kholia/Easy-Transceiver/BoB-For-2003/Screenshot_2022-04-22_13-50-55.png

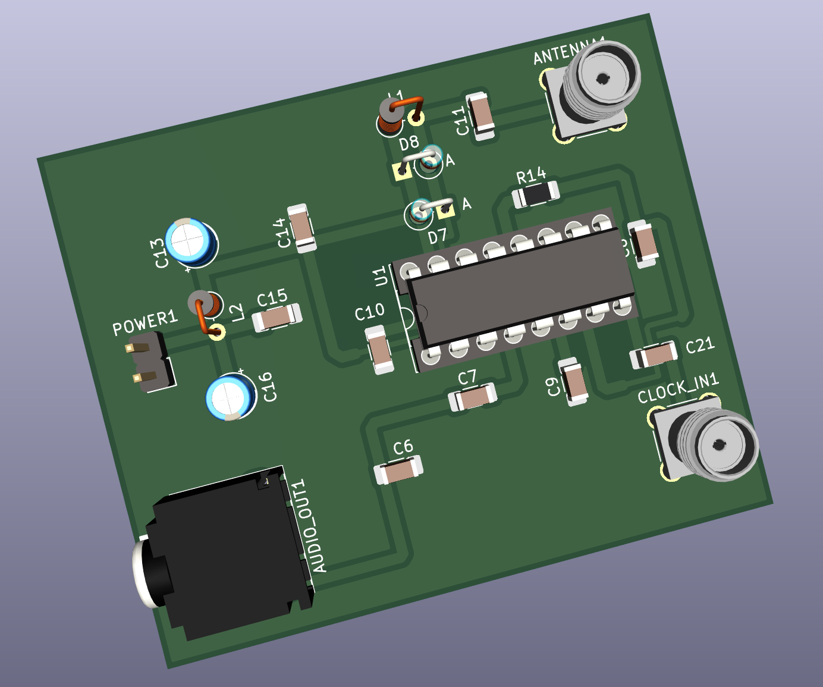
BoB-For-2003/Screenshot_2022-04-22_13-50-55.png
