kholia/Easy-Transceiver/HPF-BCI-Filter-RX/QUCS-filter/Screenshot_2022-02-17_18-40-45.png

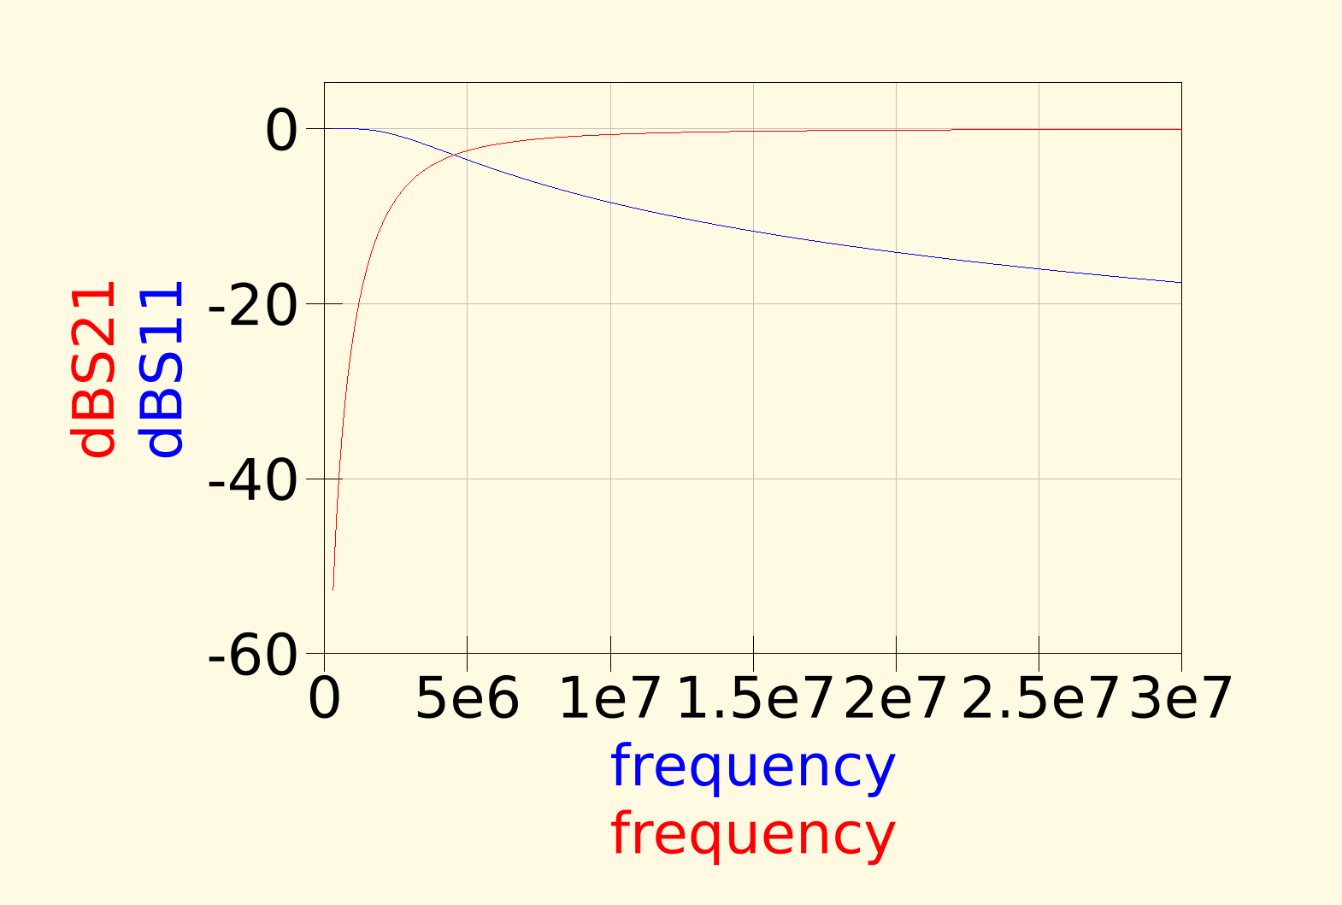
HPF-BCI-Filter-RX/QUCS-filter/Screenshot_2022-02-17_18-40-45.png
