kholia/Easy-Transceiver/images/1-CHANNEL-RELAY-MODULE-5V-Interfacing.jpg

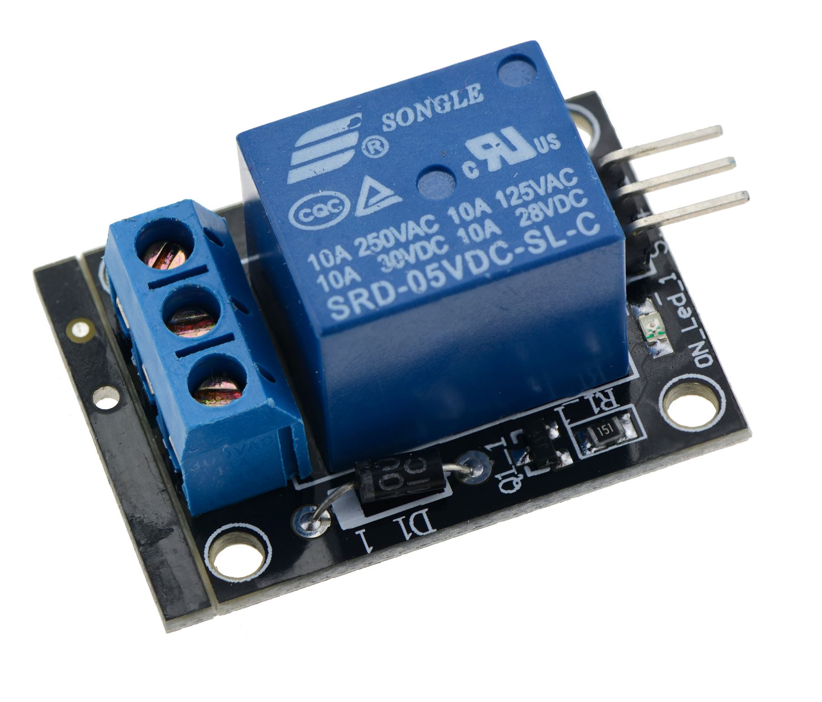
images/1-CHANNEL-RELAY-MODULE-5V-Interfacing.jpg
