kholia/Easy-Transceiver/images/3.5mm-Female-Stereo-Audio-Socket-Headphone-Jack-Connector-5-Pin-PCB-Mount_1.jpg

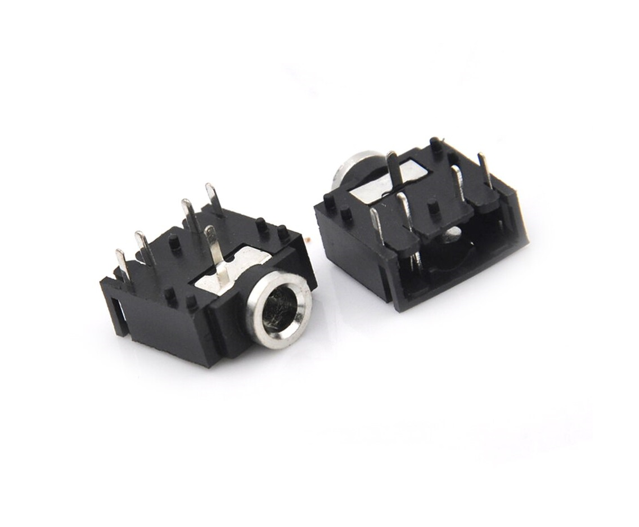
images/3.5mm-Female-Stereo-Audio-Socket-Headphone-Jack-Connector-5-Pin-PCB-Mount_1.jpg
