kholia/Easy-Transceiver/images/428.jpg

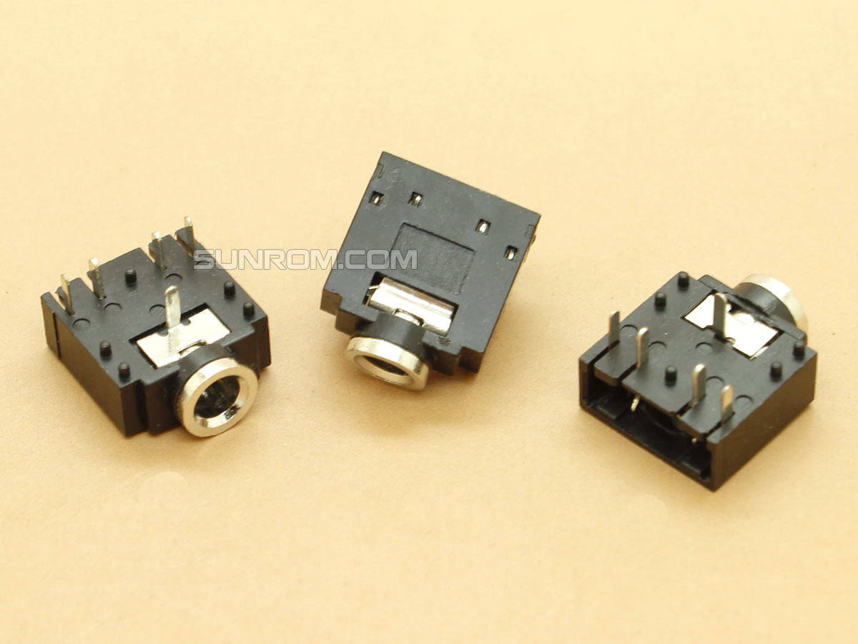
images/428.jpg
