kholia/Easy-Transceiver/images/Arduino-Nano.jpg

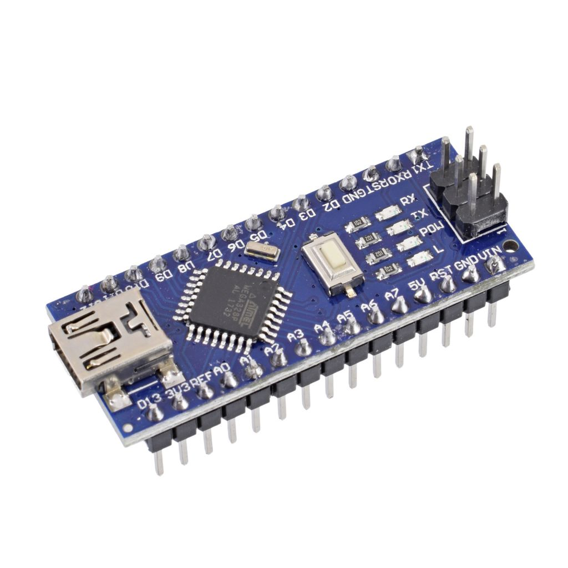
images/Arduino-Nano.jpg
