kholia/Easy-Transceiver/images/AVR ISP Programmable Expansion Shield Board.jpg

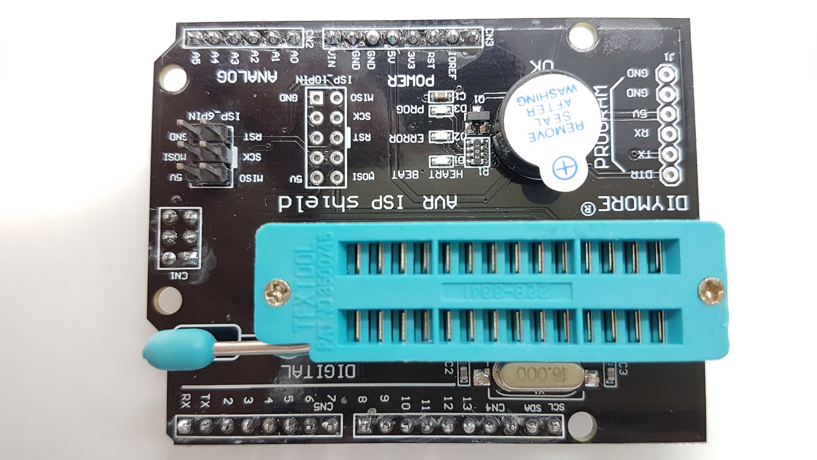
images/AVR ISP Programmable Expansion Shield Board.jpg
