kholia/Easy-Transceiver/images/DIY-USB-Cable/Sunrom-1.jpg

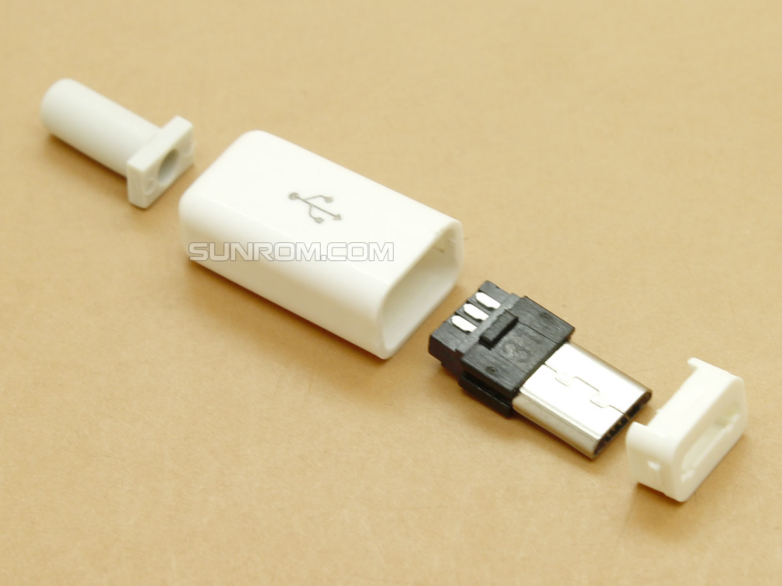
images/DIY-USB-Cable/Sunrom-1.jpg
