kholia/Easy-Transceiver/images/DIY-USB-Cable/Sunrom-2.jpg

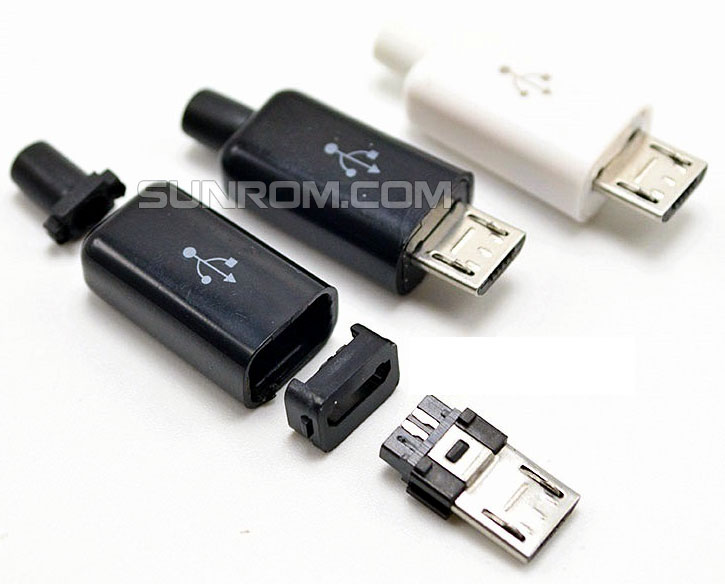
images/DIY-USB-Cable/Sunrom-2.jpg
