kholia/Easy-Transceiver/images/DIY-USB-Cable/usb-microb-plug-connector-4.jpg

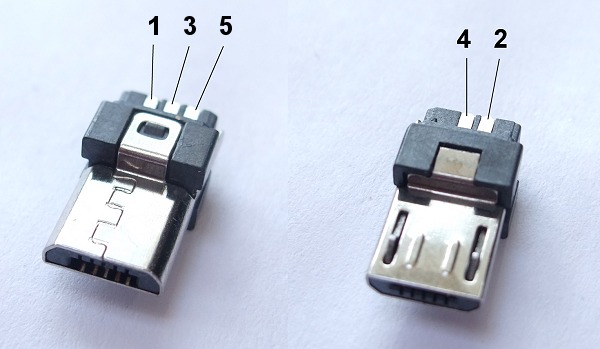
images/DIY-USB-Cable/usb-microb-plug-connector-4.jpg
