kholia/Easy-Transceiver/images/ICSP header pins.png

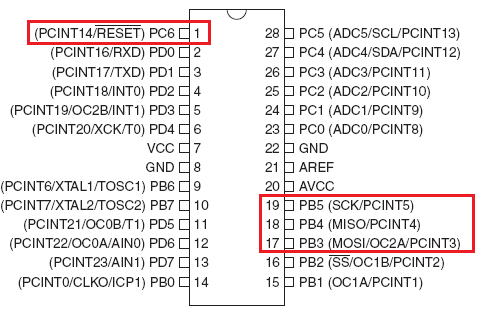
images/ICSP header pins.png
