kholia/Easy-Transceiver/images/ICSP stuff.png

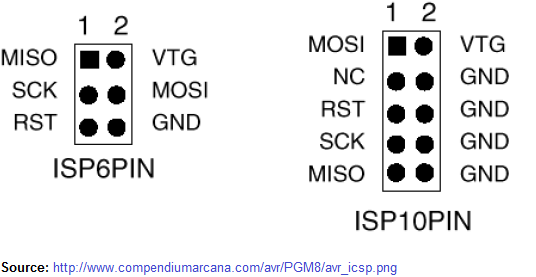
images/ICSP stuff.png
