kholia/Easy-Transceiver/images/PJ-307 photo.jpg

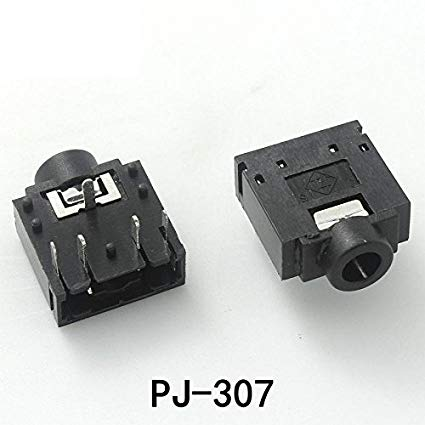
images/PJ-307 photo.jpg
