kholia/Easy-Transceiver/images/SFSS-3.5mm-5Pin-1280x720.jpg

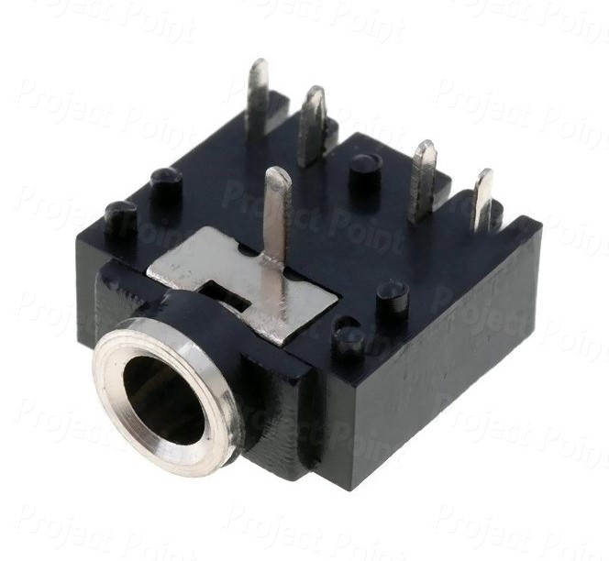
images/SFSS-3.5mm-5Pin-1280x720.jpg
