kholia/Easy-Transceiver/images/SSOP-16,SOIC-16.jpg

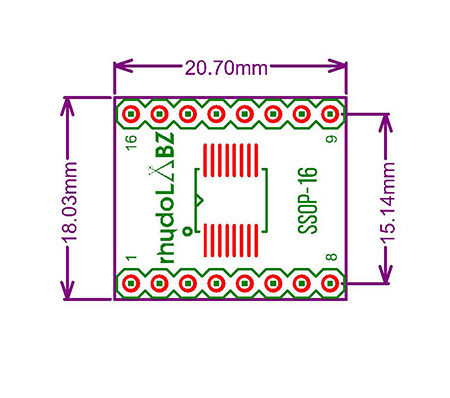
images/SSOP-16,SOIC-16.jpg
