kholia/Easy-Transceiver/images/Toshiba TA2003.jpg

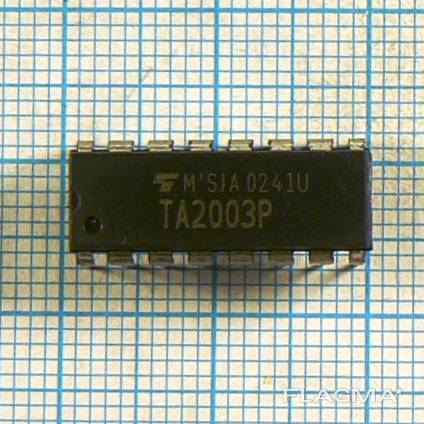
images/Toshiba TA2003.jpg
