kholia/Easy-Transceiver/images/USBaspAdapter_03.jpg

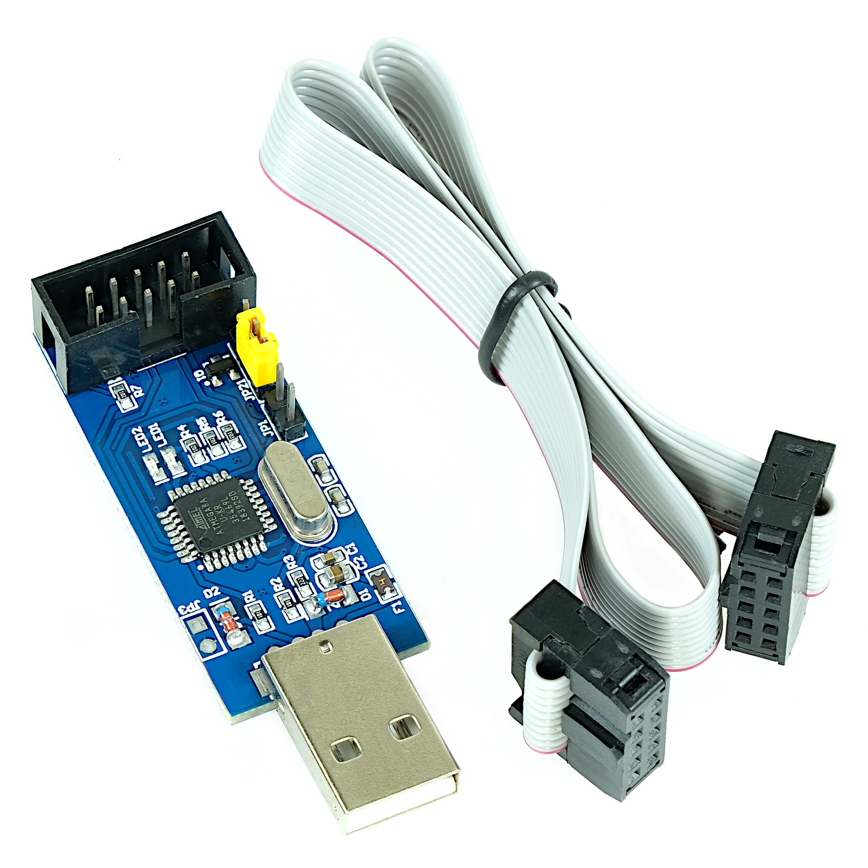
images/USBaspAdapter_03.jpg
