kholia/Easy-Transceiver/LU2HES-Photos/1.jpg

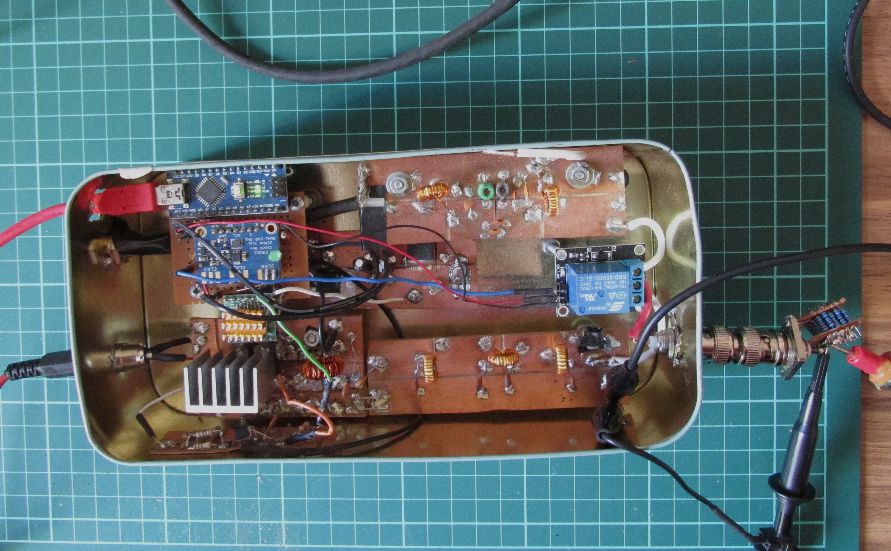
LU2HES-Photos/1.jpg
