kholia/Easy-Transceiver/LU2HES-Photos/2.jpg

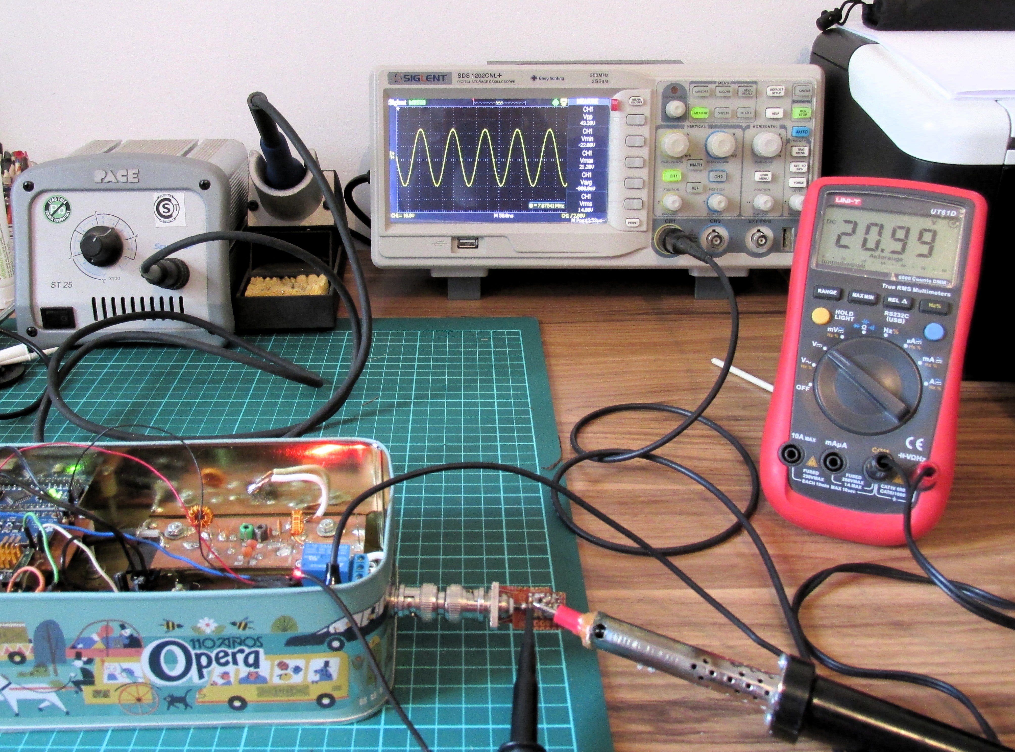
LU2HES-Photos/2.jpg
