kholia/Easy-Transceiver/PDX++/RPi-Pico-SPI-LCD_schem.png

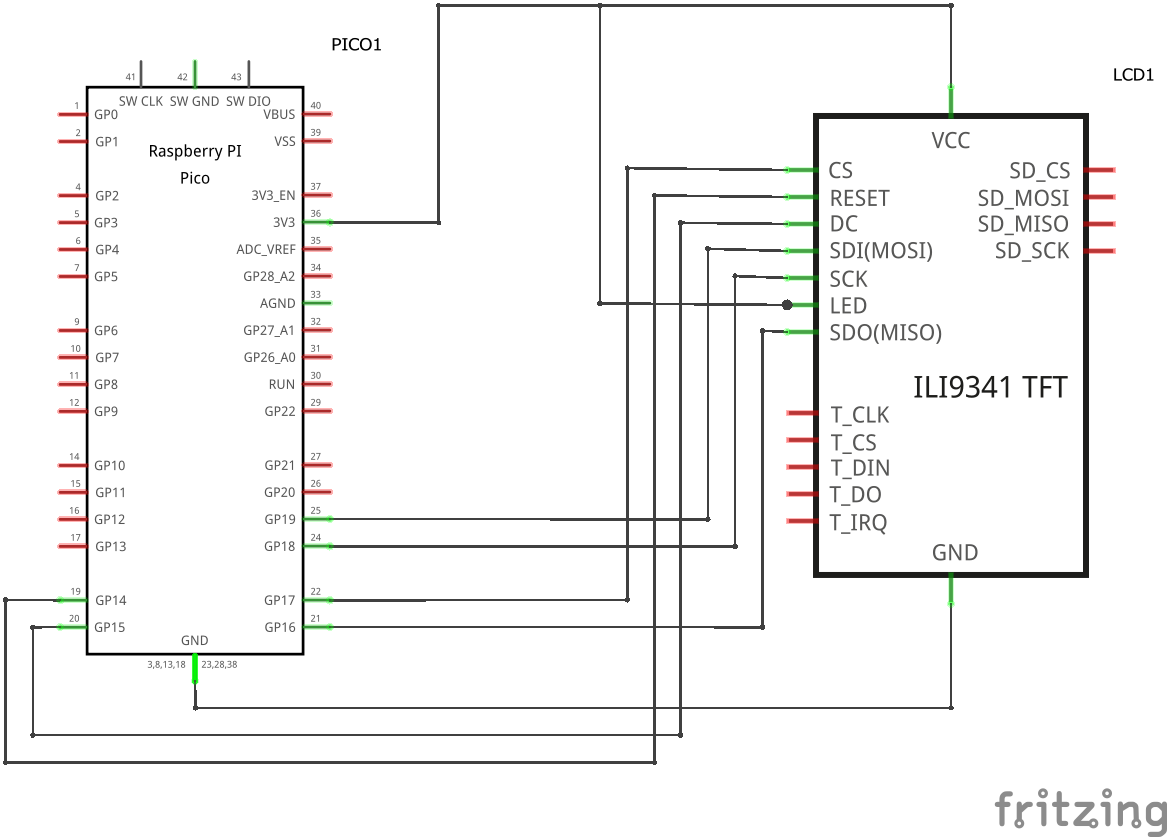
PDX++/RPi-Pico-SPI-LCD_schem.png
