kholia/Easy-Transceiver/PDX/BoB-TA2003.png

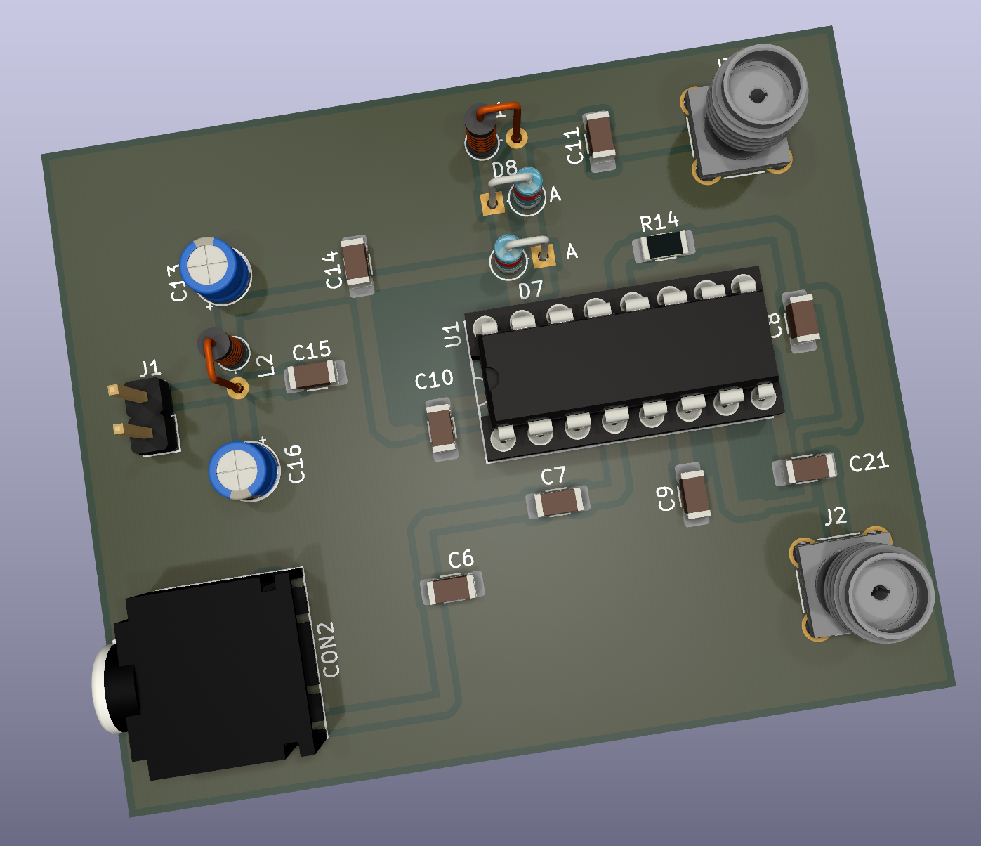
PDX/BoB-TA2003.png
