kholia/Easy-Transceiver/references/22-23-2021-_sideB.jpg

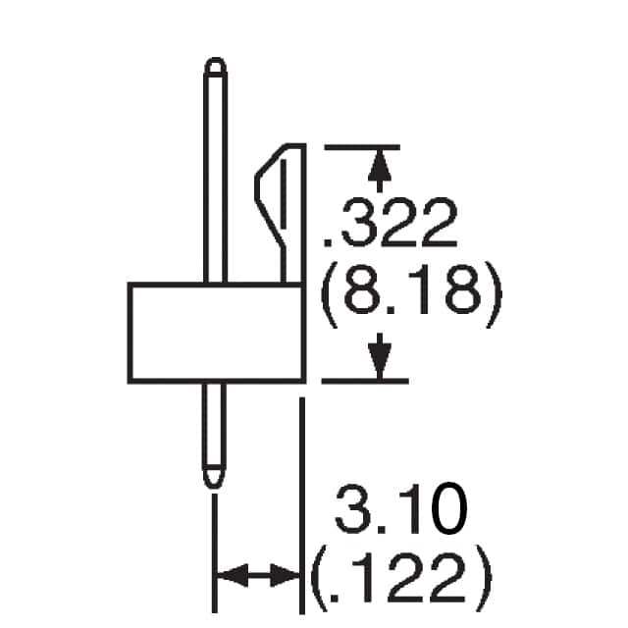
references/22-23-2021-_sideB.jpg
