kholia/Easy-Transceiver/references/dpdt-relay.png

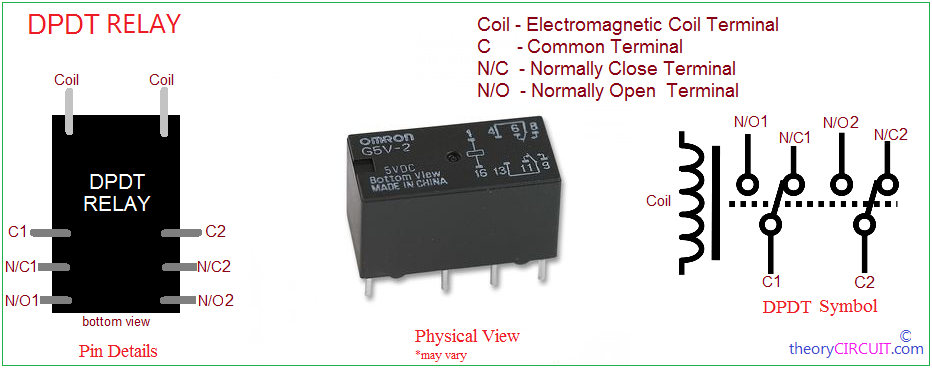
references/dpdt-relay.png
