kholia/Easy-Transceiver/references/Molex-22-23-5021.jpg

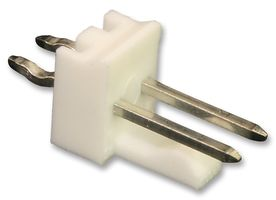
references/Molex-22-23-5021.jpg
