kholia/Easy-Transceiver/references/ShelfKey - 0022232021.jpg

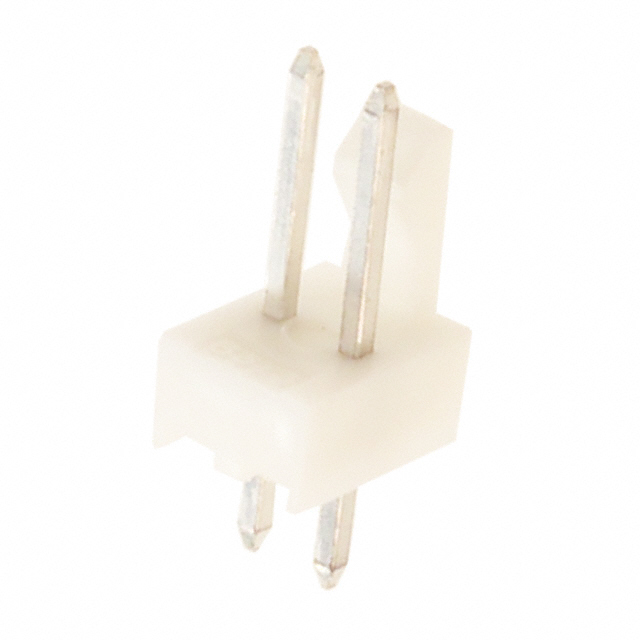
references/ShelfKey - 0022232021.jpg
