kholia/Easy-Transceiver/RX-Chain/RTL-SDR-Not-Too-Bad-Screenshot_2022-02-13_11-20-35.png

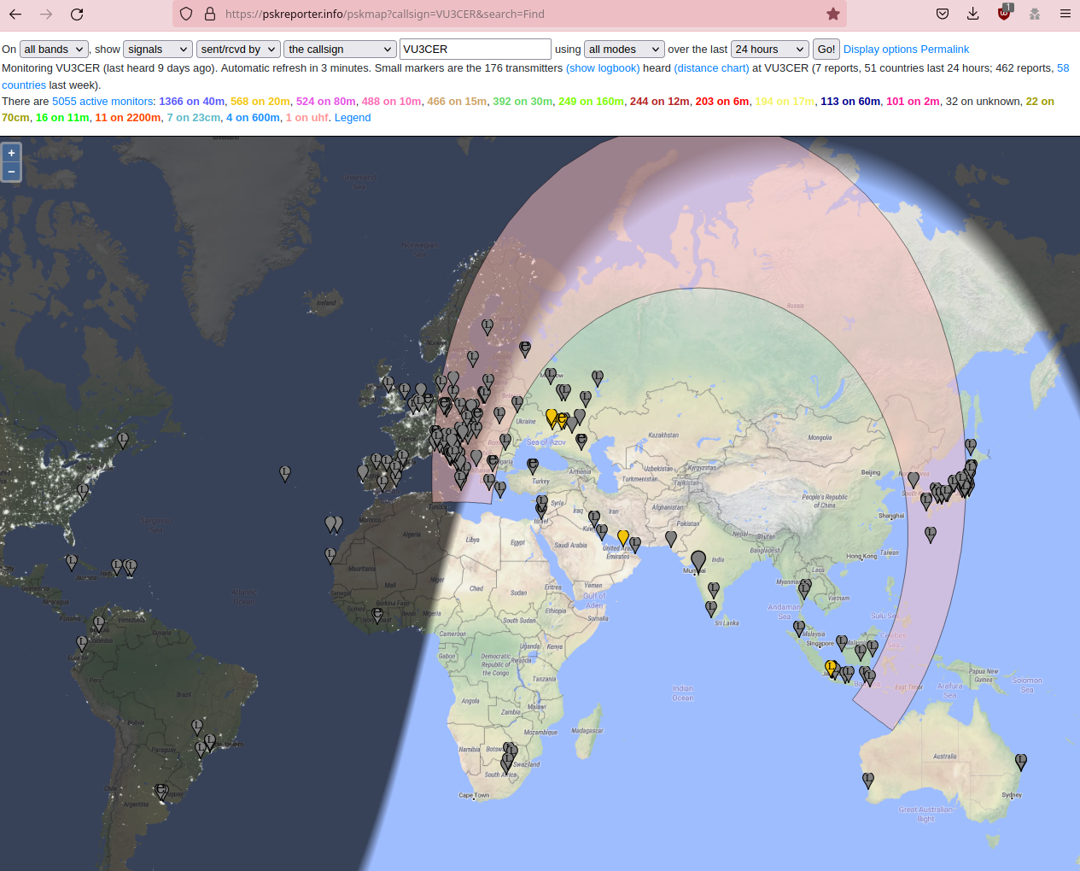
RX-Chain/RTL-SDR-Not-Too-Bad-Screenshot_2022-02-13_11-20-35.png
