kholia/Easy-Transceiver/images/DIY-USB-Cable/micro-usb-power-connector-wiring.png

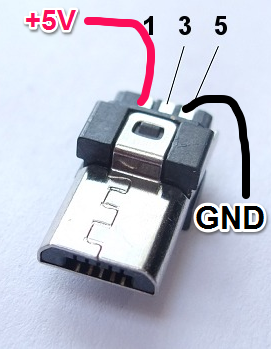
images/DIY-USB-Cable/micro-usb-power-connector-wiring.png
