kholia/Easy-Transceiver/images/DIY-USB-Cable/neverstopbuilding-blog-wiring-micro-usb-pinout.png

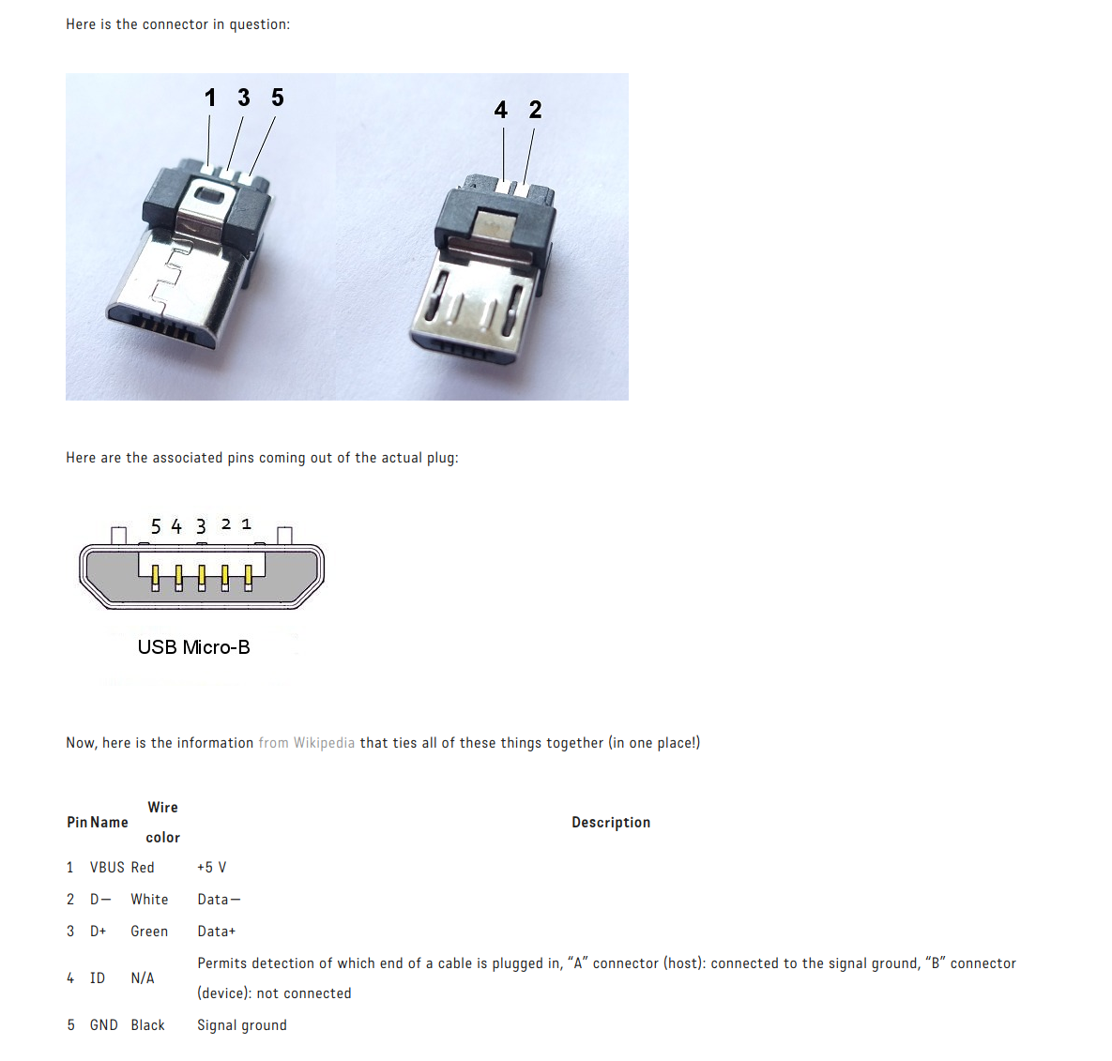
images/DIY-USB-Cable/neverstopbuilding-blog-wiring-micro-usb-pinout.png
