kholia/Easy-Transceiver/RX-Chain/Transceiver-RX-Performance/RX-Easy-Transceiver-Screenshot_2022-03-02_21-32-30.png

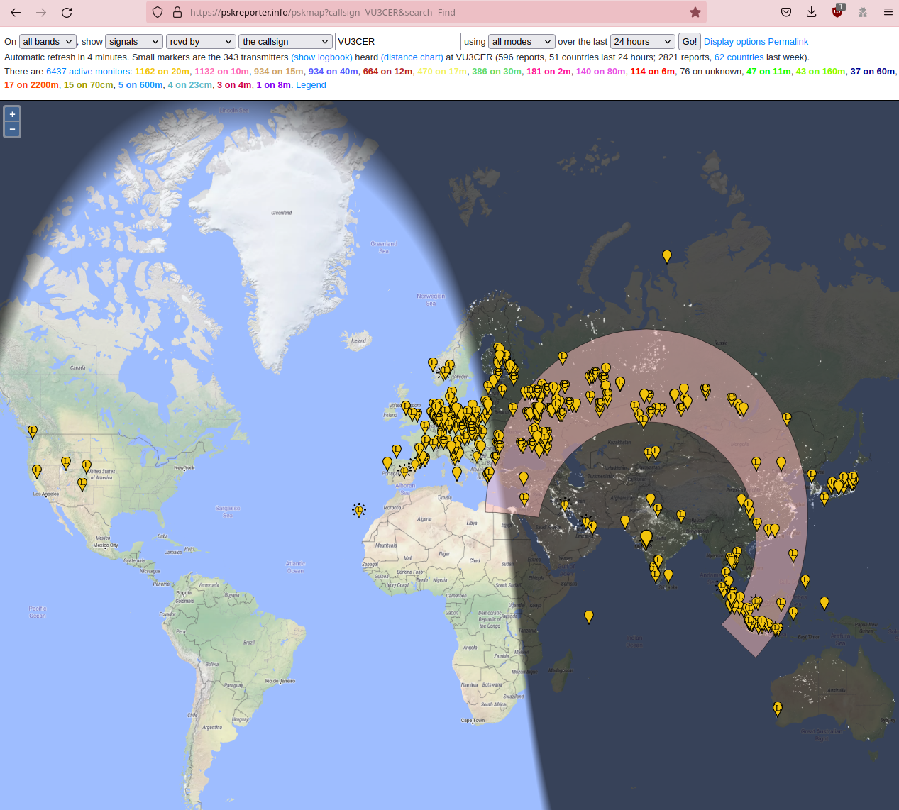
RX-Chain/Transceiver-RX-Performance/RX-Easy-Transceiver-Screenshot_2022-03-02_21-32-30.png
